julowe/fire-pumpkin/glade-dispenser/glade-gears.JPEG

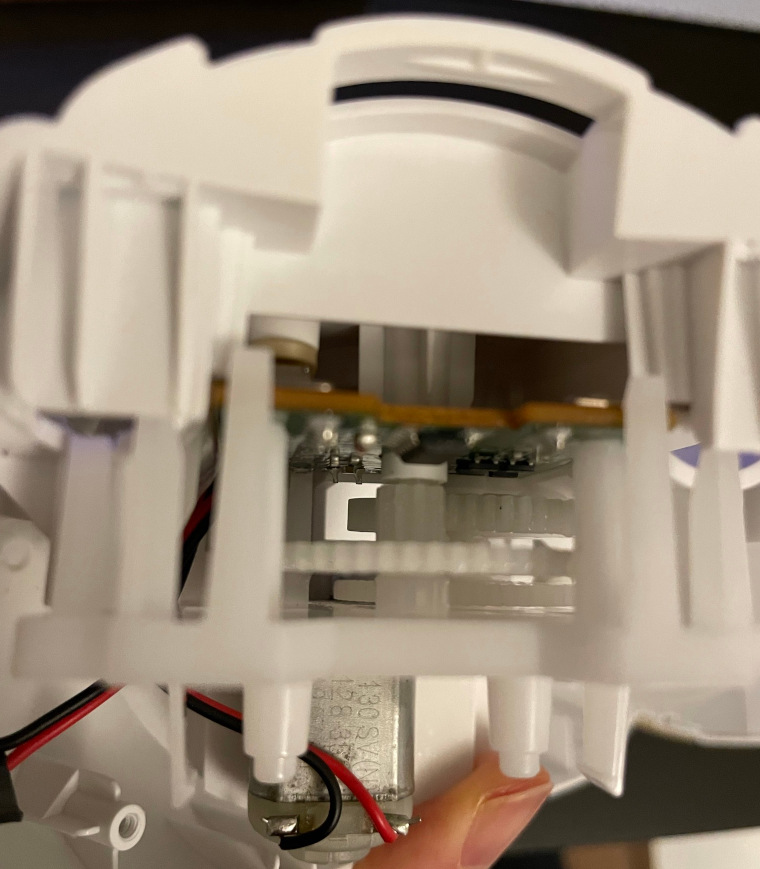
glade-dispenser/glade-gears.JPEG
