julowe/fire-pumpkin/glade-dispenser/glade-motor.JPEG

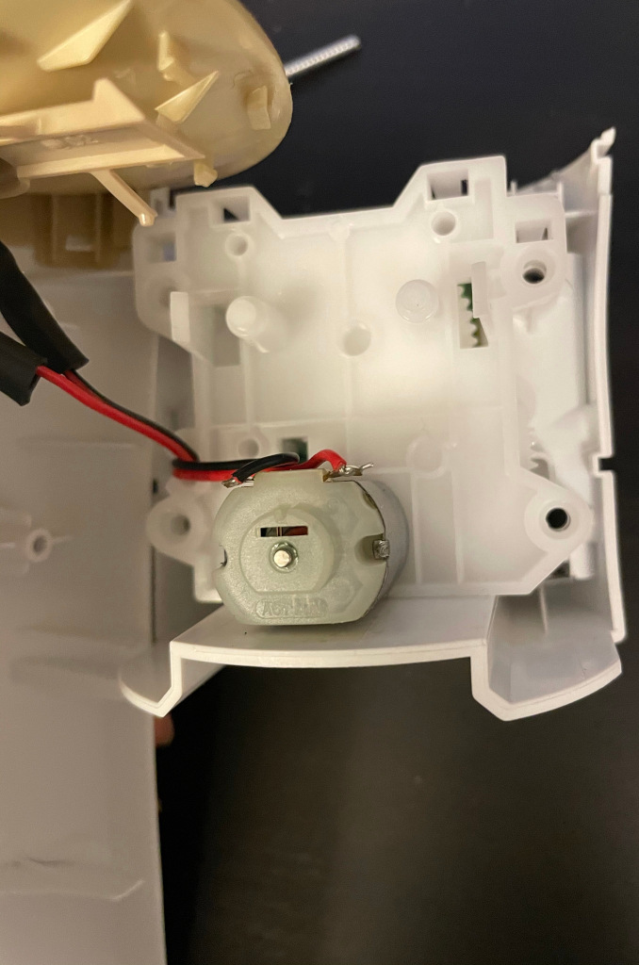
glade-dispenser/glade-motor.JPEG
