julowe/fire-pumpkin/glade-dispenser/glade-wires-button.JPEG

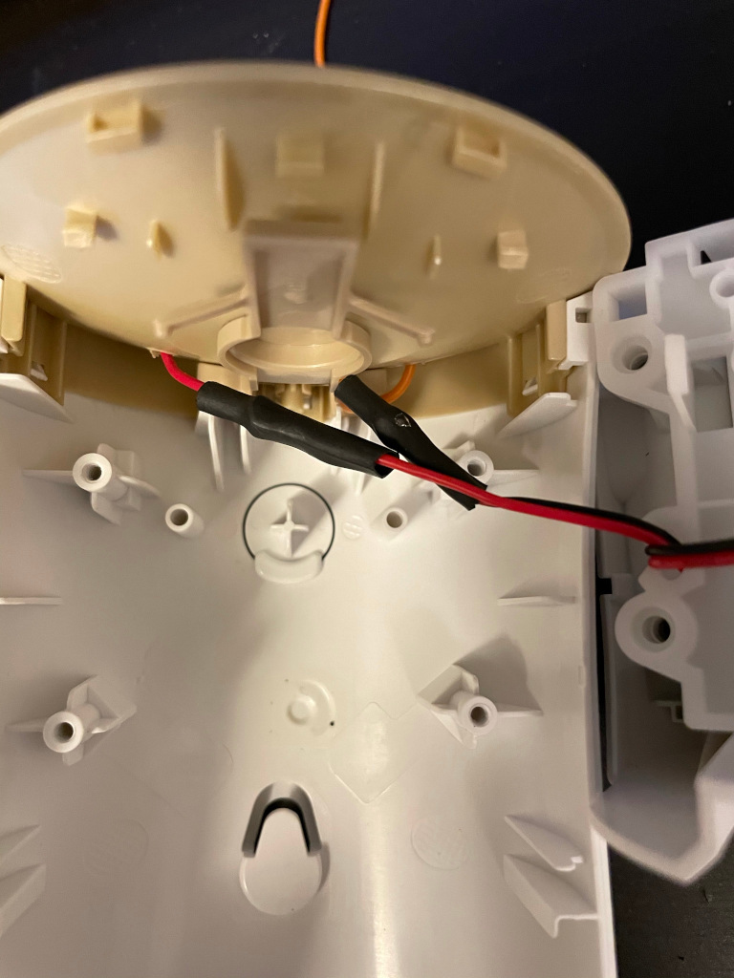
glade-dispenser/glade-wires-button.JPEG
